SherimaX/Claude-Watch/stl/setting_shaft.stl

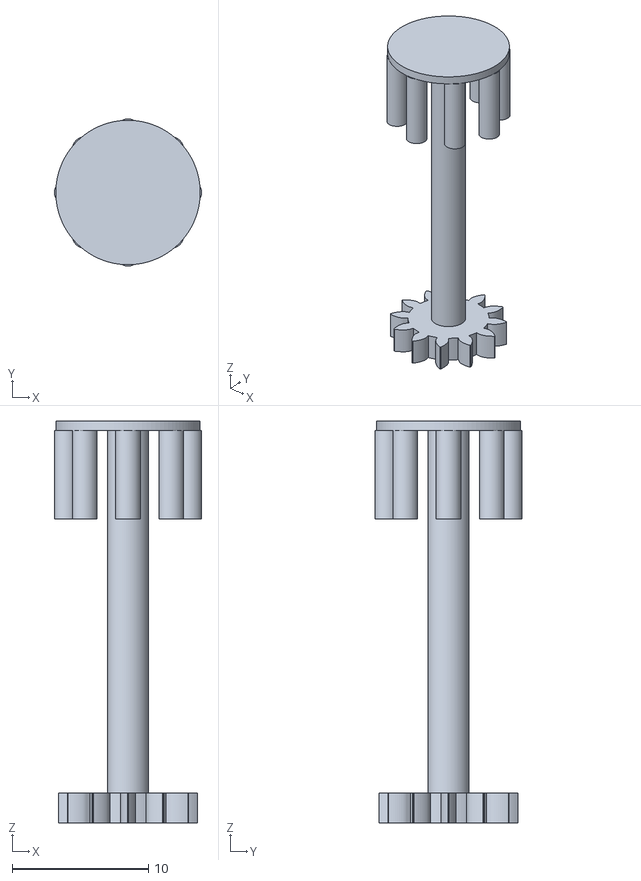
[picture p23: CAD file, 2026-06-10]
stl/setting_shaft.stl
10.8 x 10.8 x 29.5
