SherimaX/Claude-Watch/stl/crown_tube.stl

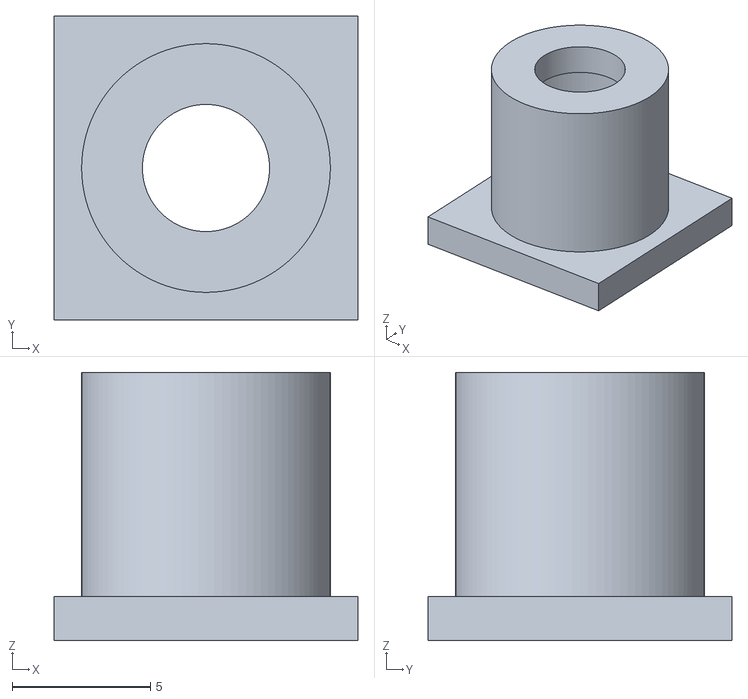
[picture p24: CAD file, 2026-06-10]
stl/crown_tube.stl
11.0 x 11.0 x 9.70
