SherimaX/Claude-Watch/stl/case_back.stl

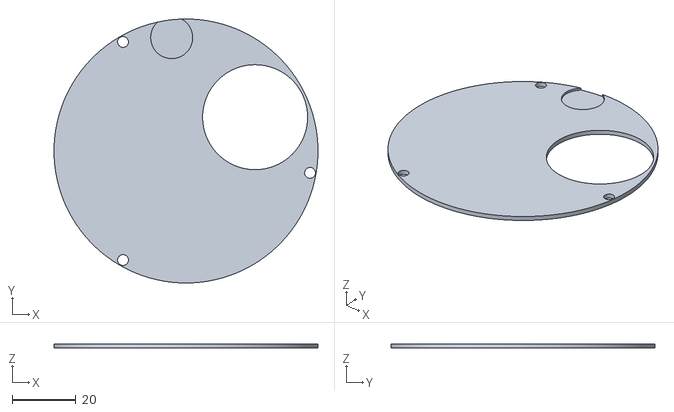
[picture p25: CAD file, 2026-06-10]
stl/case_back.stl
83.0 x 83.0 x 1.40
