SherimaX/Claude-Watch/stl/ratchet_wheel.stl

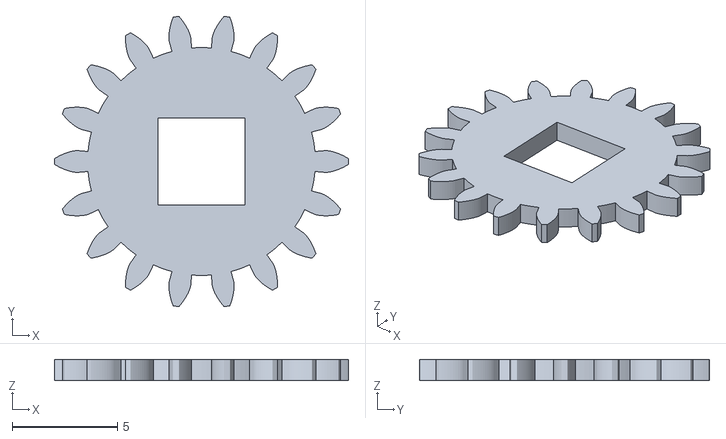
[picture p26: CAD file, 2026-06-10]
stl/ratchet_wheel.stl
14.0 x 13.8 x 1.00
