SherimaX/Claude-Watch/stl/crown.stl

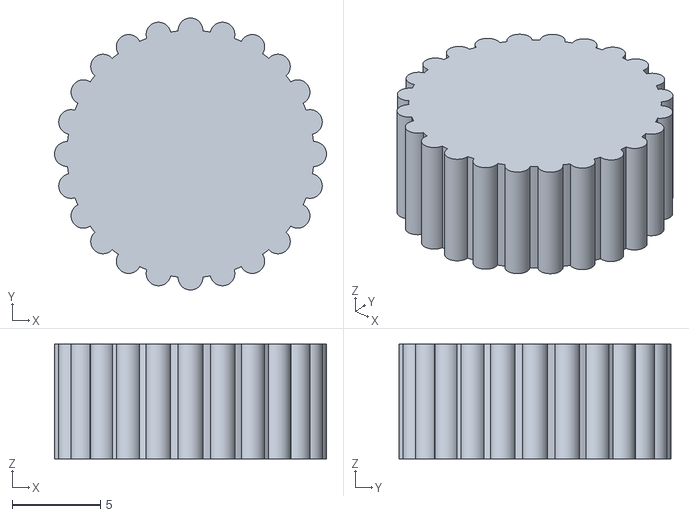
[picture p27: CAD file, 2026-06-10]
stl/crown.stl
15.4 x 15.4 x 6.50
