SherimaX/Claude-Watch/stl/barrel_arbor.stl

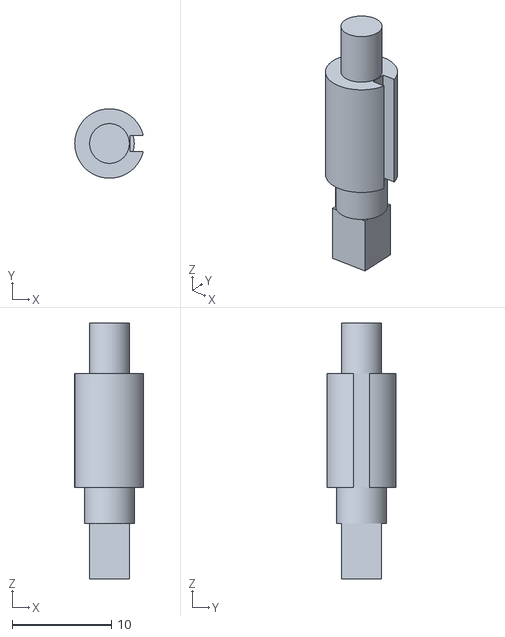
[picture p28: CAD file, 2026-06-10]
stl/barrel_arbor.stl
6.91 x 7.00 x 25.8
