SherimaX/Claude-Watch/stl/barrel_drum.stl

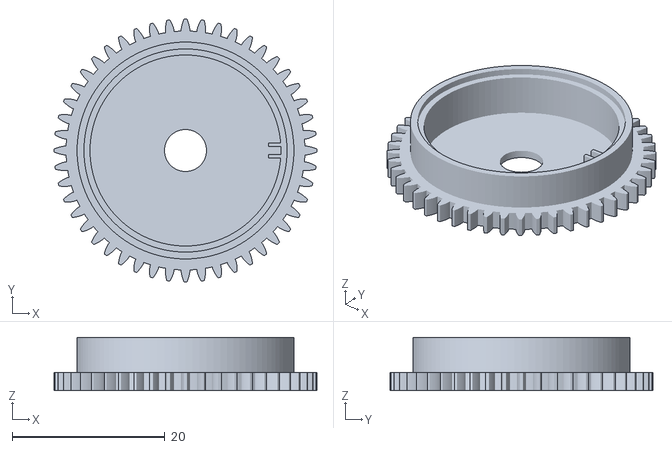
[picture p29: CAD file, 2026-06-10]
stl/barrel_drum.stl
34.4 x 34.4 x 7.00
