SherimaX/Claude-Watch/stl/case_ring.stl

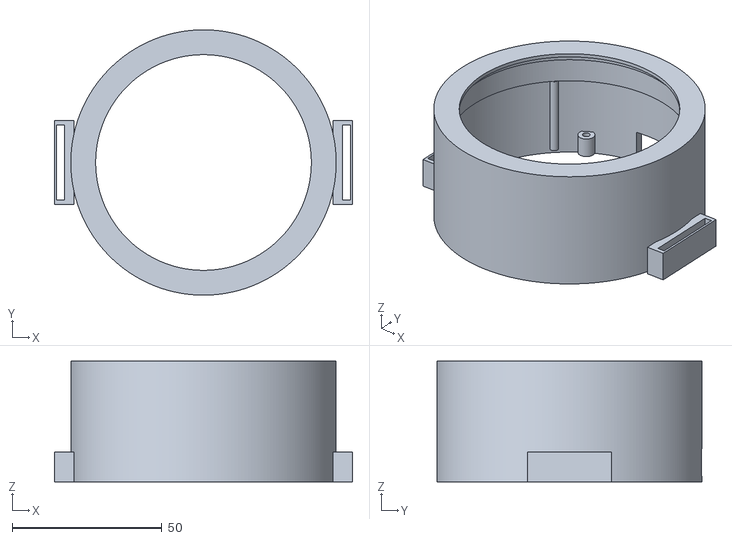
[picture p30: CAD file, 2026-06-10]
stl/case_ring.stl
99.5 x 88.6 x 40.4
