SherimaX/Claude-Watch/stl/barrel_lid.stl

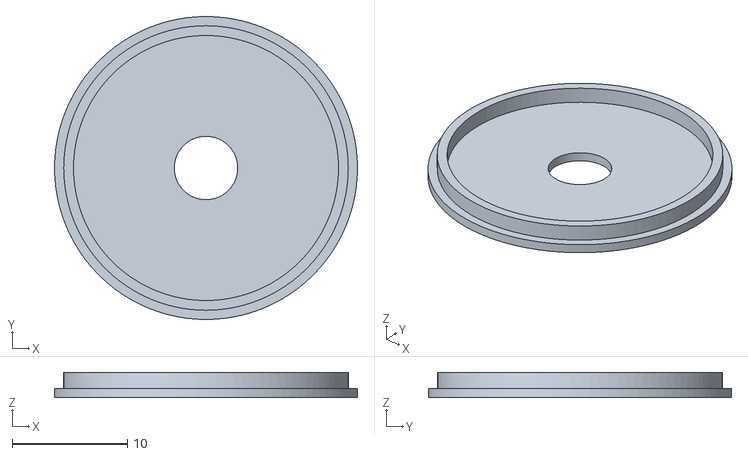
[picture p31: CAD file, 2026-06-10]
stl/barrel_lid.stl
26.3 x 26.3 x 2.20
