SherimaX/Claude-Watch/stl/stem.stl

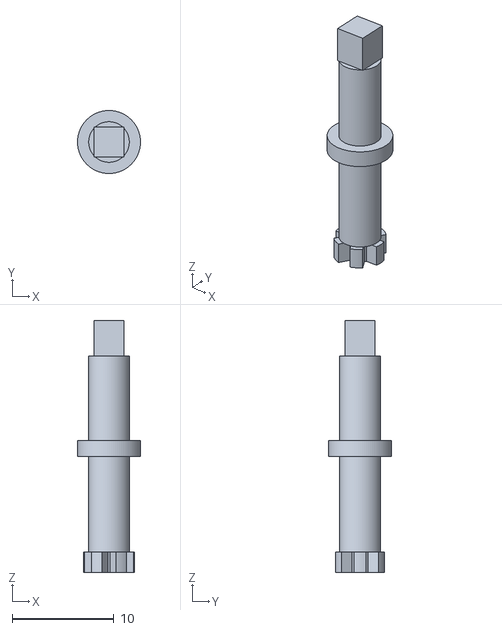
[picture p32: CAD file, 2026-06-10]
stl/stem.stl
6.20 x 6.20 x 24.8
