SherimaX/Claude-Watch/stl/click.stl

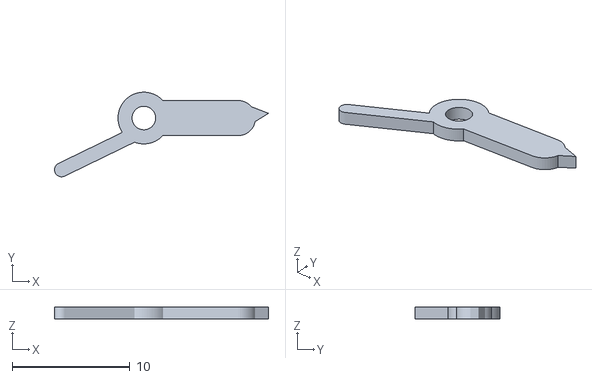
[picture p33: CAD file, 2026-06-10]
stl/click.stl
18.2 x 7.20 x 1.00
