SherimaX/Claude-Watch/stl/crown_wheel.stl

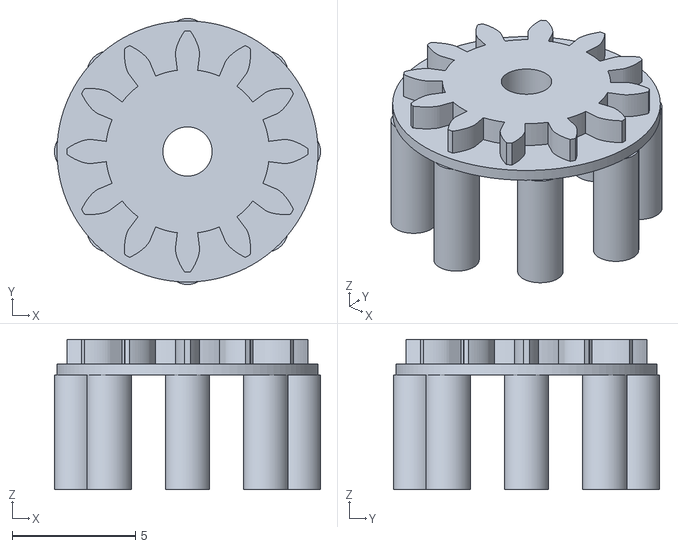
[picture p34: CAD file, 2026-06-10]
stl/crown_wheel.stl
10.8 x 10.8 x 6.10
