SherimaX/Claude-Watch/stl/hairspring_soft.stl

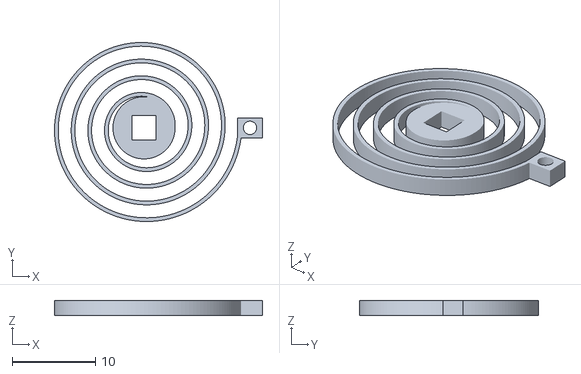
[picture p35: CAD file, 2026-06-10]
stl/hairspring_soft.stl
24.9 x 21.5 x 1.80
