SherimaX/Claude-Watch/stl/minute_hand.stl

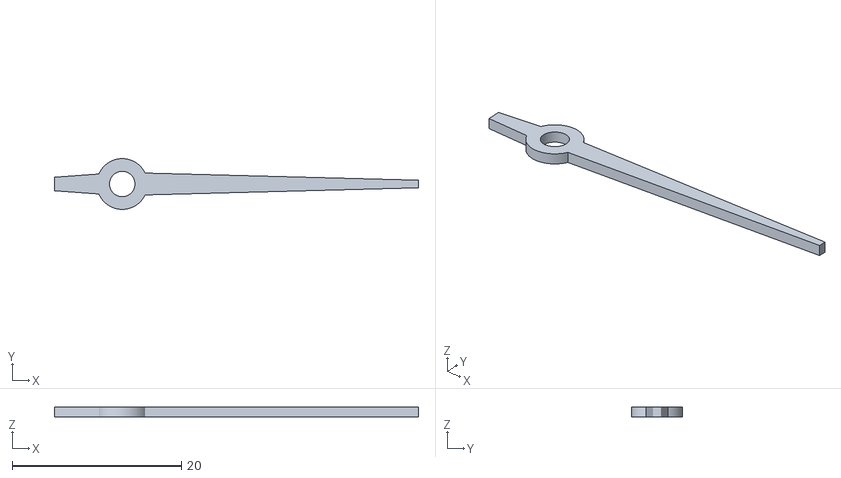
[picture p36: CAD file, 2026-06-10]
stl/minute_hand.stl
43.0 x 6.00 x 1.20
