SherimaX/Claude-Watch/stl/escape_wheel.stl

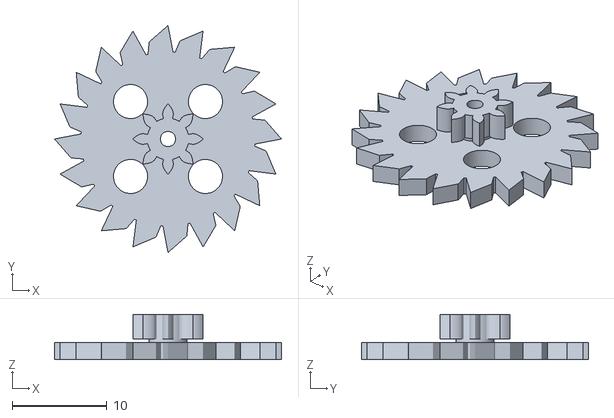
[picture p37: CAD file, 2026-06-10]
stl/escape_wheel.stl
24.0 x 24.0 x 4.80
