SherimaX/Claude-Watch/stl/center_arbor.stl

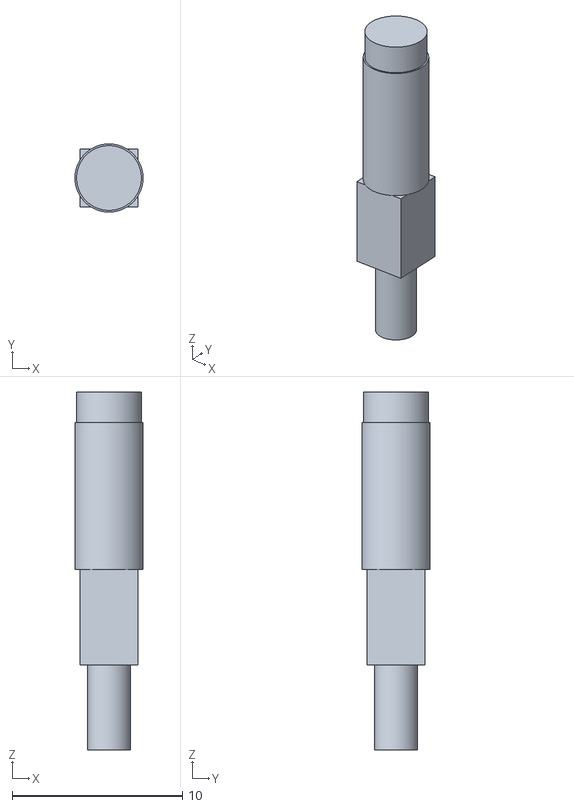
[picture p38: CAD file, 2026-06-10]
stl/center_arbor.stl
4.00 x 4.00 x 21.0
