SherimaX/Claude-Watch/stl/hairspring_stiff.stl

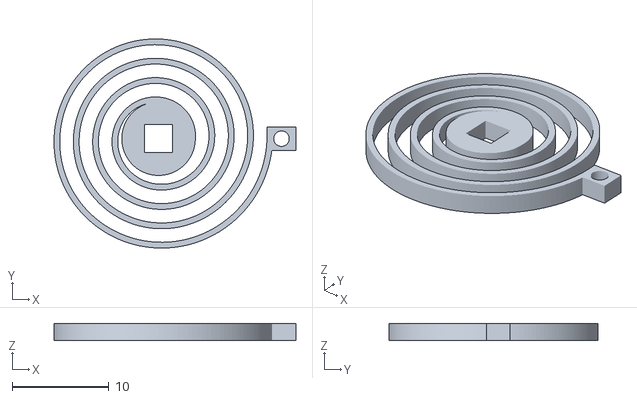
[picture p39: CAD file, 2026-06-10]
stl/hairspring_stiff.stl
25.0 x 21.6 x 1.80
