SherimaX/Claude-Watch/stl/hour_wheel.stl

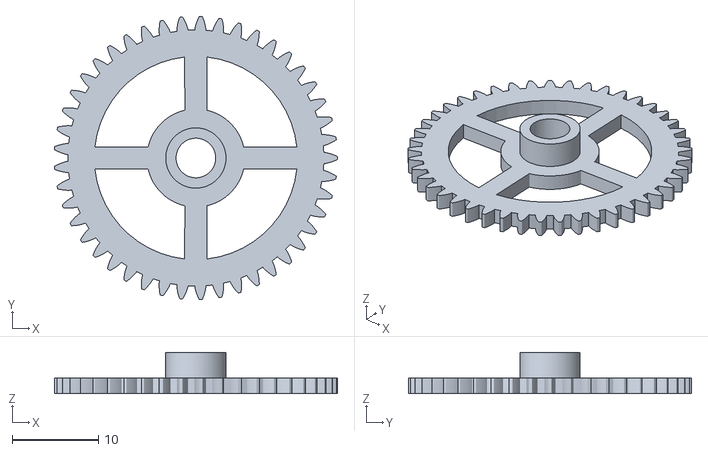
[picture p40: CAD file, 2026-06-10]
stl/hour_wheel.stl
32.9 x 32.9 x 4.80
