SherimaX/Claude-Watch/stl/roller_safety.stl

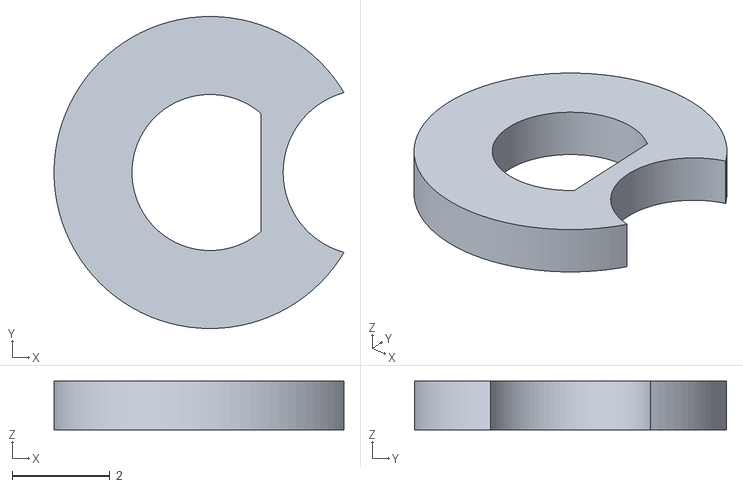
[picture p41: CAD file, 2026-06-10]
stl/roller_safety.stl
5.95 x 6.40 x 1.00
