SherimaX/Claude-Watch/stl/minute_wheel.stl

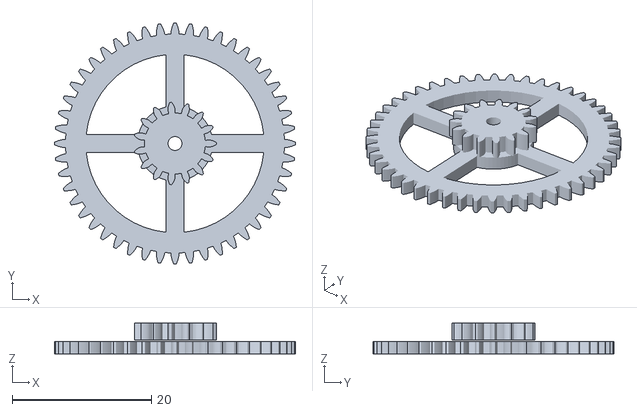
[picture p42: CAD file, 2026-06-10]
stl/minute_wheel.stl
34.6 x 34.6 x 4.40
