SherimaX/Claude-Watch/stl/fourth_wheel.stl

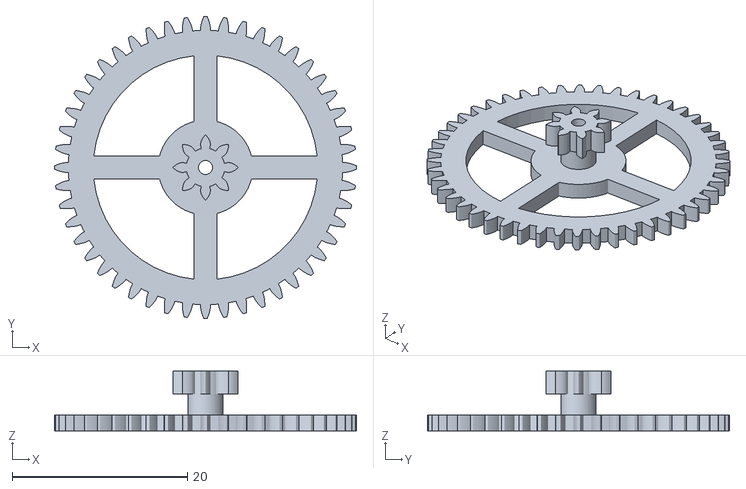
[picture p43: CAD file, 2026-06-10]
stl/fourth_wheel.stl
34.4 x 34.4 x 6.80
