SherimaX/Claude-Watch/stl/third_wheel.stl

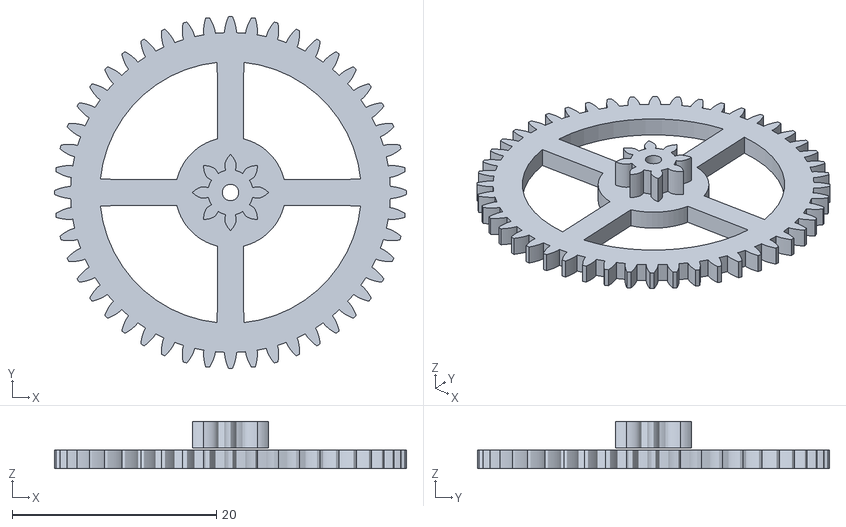
[picture p44: CAD file, 2026-06-10]
stl/third_wheel.stl
34.4 x 34.4 x 4.60
