SherimaX/Claude-Watch/stl/center_wheel.stl

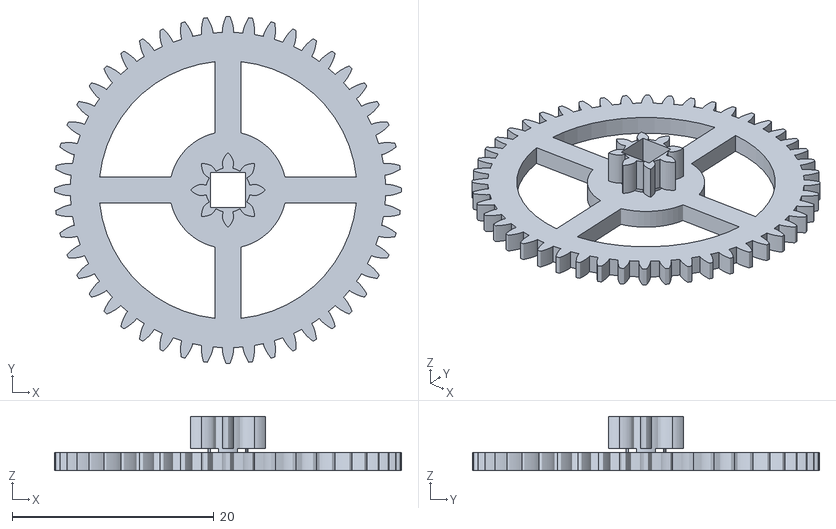
[picture p45: CAD file, 2026-06-10]
stl/center_wheel.stl
34.4 x 34.4 x 5.40
