SherimaX/Claude-Watch/stl/balance_arbor.stl

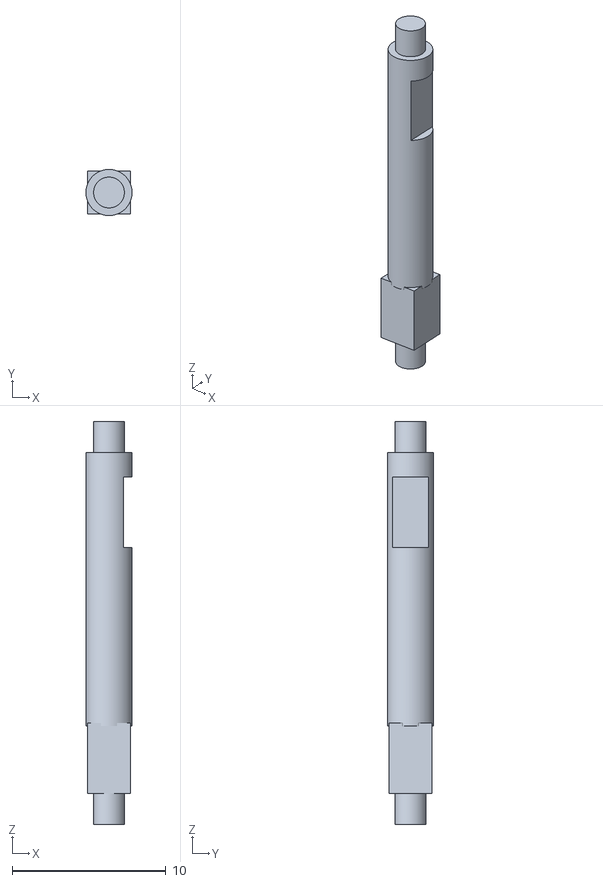
[picture p46: CAD file, 2026-06-10]
stl/balance_arbor.stl
3.00 x 3.00 x 26.2
