SherimaX/Claude-Watch/stl/cannon_pinion.stl

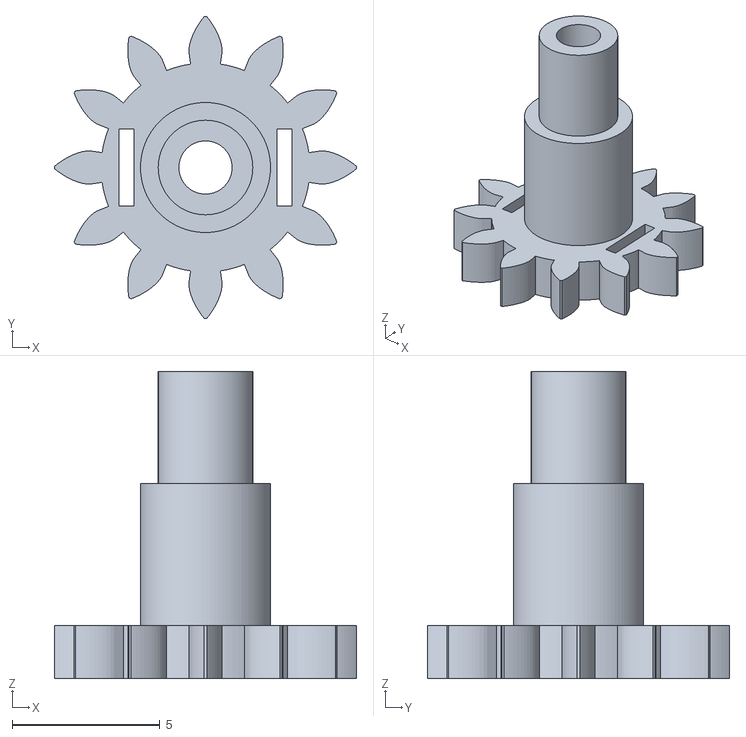
[picture p47: CAD file, 2026-06-10]
stl/cannon_pinion.stl
10.2 x 10.2 x 10.4
