SherimaX/Claude-Watch/stl/lever.stl

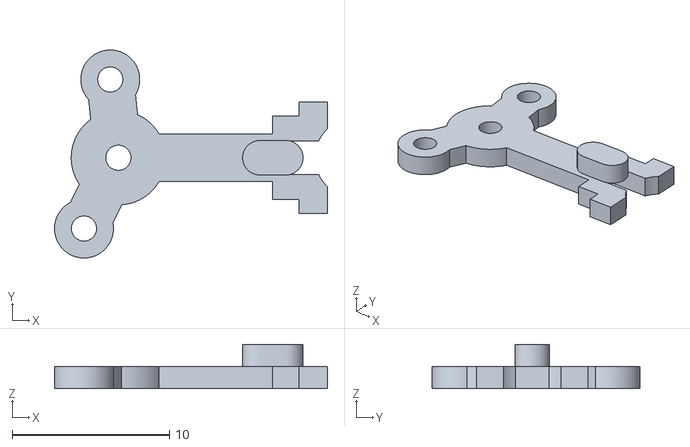
[picture p48: CAD file, 2026-06-10]
stl/lever.stl
17.4 x 13.2 x 2.80
